ElektorLabs/lora-sensor-node/src/lora-sensor-node/config.ino

#define LED_BUILTIN 5
#define RX_2 9
#define TX_2 10


// Voltage divider resistors
#define R1  218400.0 // 220k ohm 
#define R2  222200.0 // 220k ohm

#define VOFFSET 0.03 // Voltage offset for calibration
